sullyjason/MoodLogger/EmotionTracker_PCF8523/Dummy device/Dummy device.kicad_sch

## KiCad design EmotionTracker_PCF8523/Dummy device/Dummy device.kicad_sch (2026-07-07)

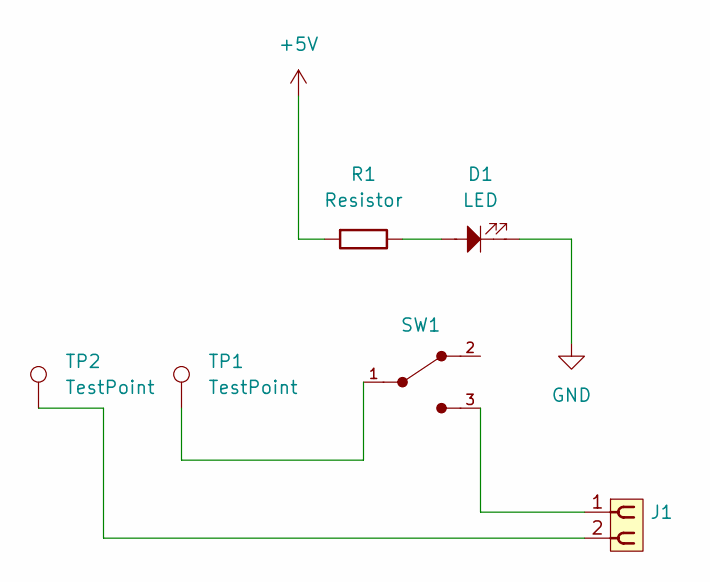
[picture p7: schematic Dummy device.kicad_sch]

Parts:
D1: LED; LED_D3.0mm_Horizontal_O6.35mm_Z10.0mm
J1: PINHD_1x2_Female; PinSocket_1x02_P2.54mm_Vertical
R1: Resistor; R_Axial_DIN0207_L6.3mm_D2.5mm_P10.16mm_Horizontal
SW1: Slide_Switch_SPDT_P3mm_10x5x10mm; SW_Slide_SPDT_Angled_CK_OS102011MA1Q
TP1, TP2: TestPoint

Connections:
+5V: R1.1
GND: D1.1
unnamed: D1.2, R1.2
unnamed: J1.1, SW1.3
unnamed: J1.2, TP2.1
unnamed: SW1.1, TP1.1
